Hi30MC/icarus/ergogen/output/outlines/leftcasecutout.dxf

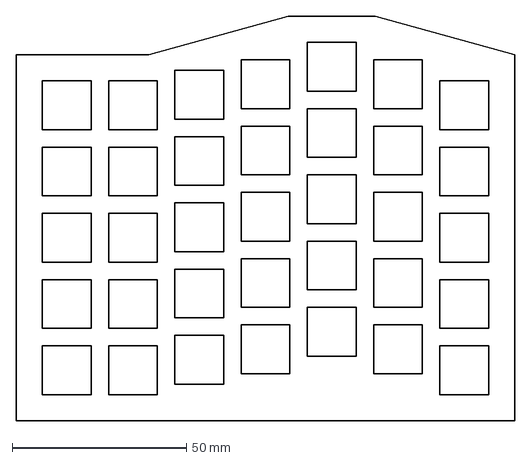
[picture p15: CAD file, 2026-05-19]
ergogen/output/outlines/leftcasecutout.dxf
143.0 x 116.0 mm
