Hi30MC/icarus/final_pcbs/components/SSSS811101.STEP

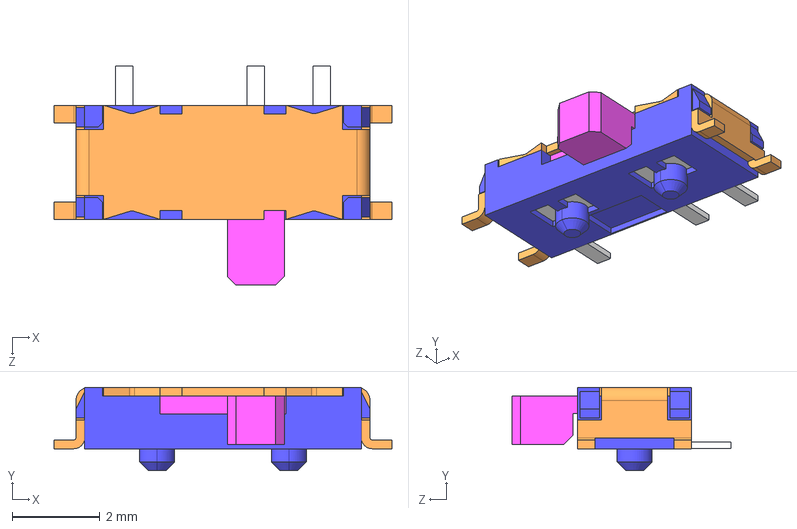
[picture p16: CAD file, 2026-06-05]
final_pcbs/components/SSSS811101.STEP
7.70 x 1.90 x 5.00 mm
