Hi30MC/icarus/ergogen/output/outlines/keys.dxf

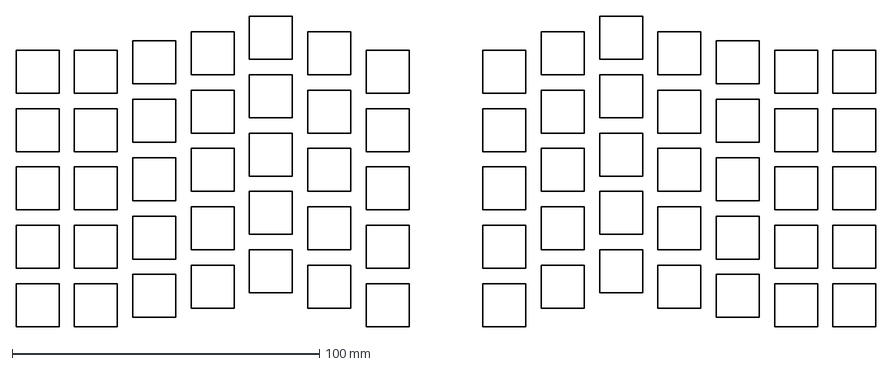
[picture p17: CAD file, 2026-05-19]
ergogen/output/outlines/keys.dxf
280.0 x 101.0 mm
