Hi30MC/icarus/final_pcbs/components/S2B-PH-K-S(LF)(SN).STEP

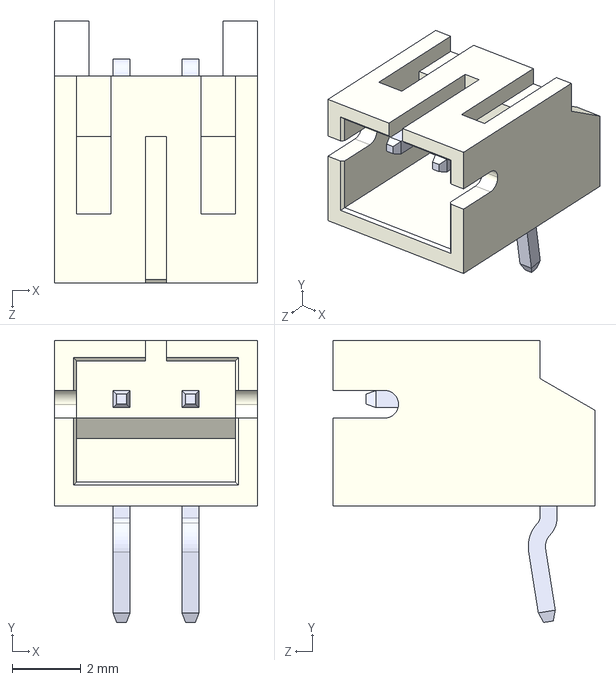
[picture p18: CAD file, 2026-06-05]
final_pcbs/components/S2B-PH-K-S(LF)(SN).STEP
5.90 x 8.18 x 7.60 mm
