Hi30MC/icarus/ergogen/output/outlines/leftboard.dxf

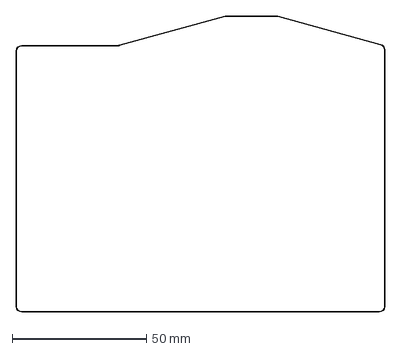
[picture p19: CAD file, 2026-05-19]
ergogen/output/outlines/leftboard.dxf
137.0 x 110.0 mm
