Hi30MC/icarus/final_pcbs/components/EVQPUL02K.stp

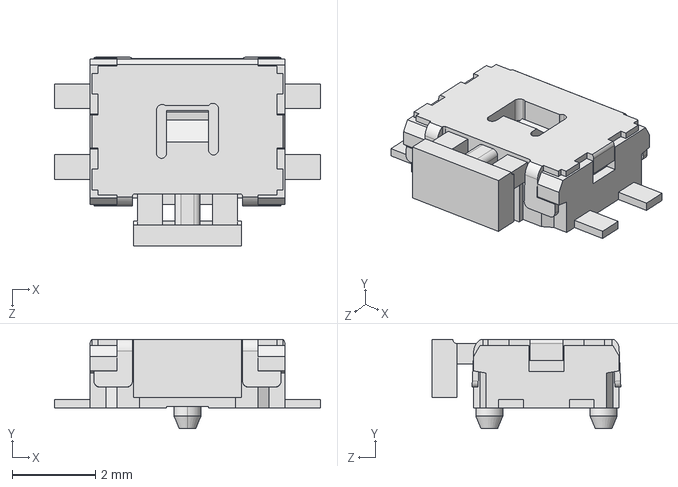
[picture p20: CAD file, 2026-06-05]
final_pcbs/components/EVQPUL02K.stp
6.40 x 2.15 x 4.54 mm
